maxoshe/ReactiveLoad/spice/16ohm simulation.asc

Amp: voltage; SINE(); AC 28
C1: cap; 200µ
C2: cap; 200µ
L1: ind; 0.47m
L2: ind; 10m
L3: ind; 0.47m
L4: ind; 10m
R1: res; 8
R2: res; 50
R3: res; 75
R4: res; 10k
R5: res; 1k
R6: res; 8
R7: res; 50
R8: res; 75
Named nets: 0, lineOut, Amp
.op
.ac oct 100 1 20000
